inn-goose/eeprom-api-arduino/wiring/kicad/eeprom_programmer/eeprom_programmer.kicad_sch

## KiCad design wiring/kicad/eeprom_programmer/eeprom_programmer.kicad_sch (2025-12-24)

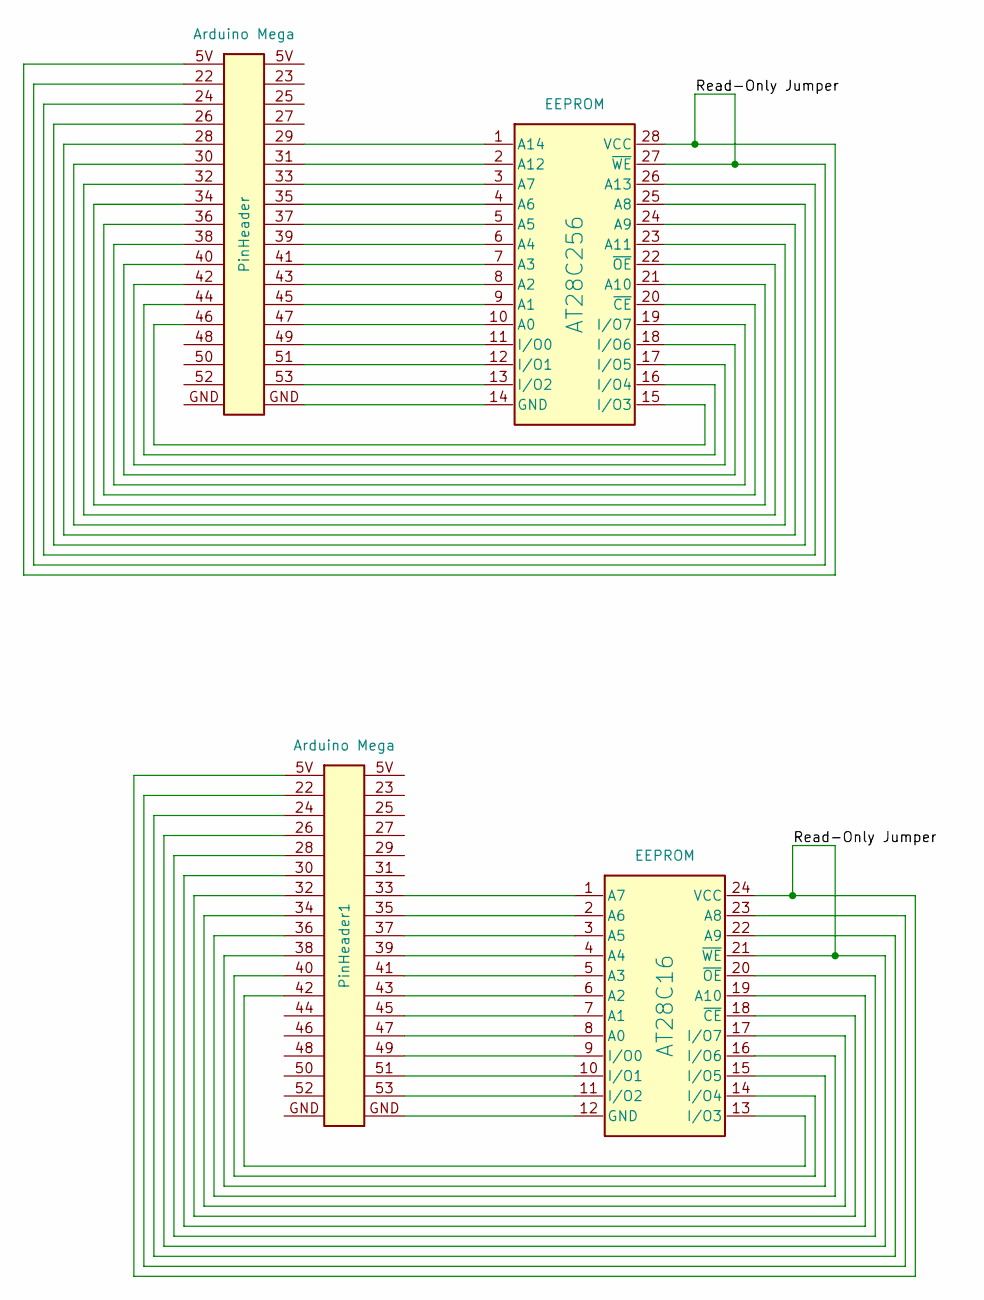
[picture p8: schematic eeprom_programmer.kicad_sch]

Parts:
AT28C16, AT28C256: EEPROM
PinHeader, PinHeader1: Arduino Mega

Connections:
unnamed: AT28C16.1 (A7), PinHeader1.33
unnamed: AT28C16.2 (A6), PinHeader1.35
unnamed: AT28C16.3 (A5), PinHeader1.37
unnamed: AT28C16.4 (A4), PinHeader1.39
unnamed: AT28C16.5 (A3), PinHeader1.41
unnamed: AT28C16.6 (A2), PinHeader1.43
unnamed: AT28C16.7 (A1), PinHeader1.45
unnamed: AT28C16.8 (A0), PinHeader1.47
unnamed: AT28C16.9 (I/O0), PinHeader1.49
unnamed: AT28C16.10 (I/O1), PinHeader1.51
unnamed: AT28C16.11 (I/O2), PinHeader1.53
unnamed: AT28C16.12 (GND), PinHeader1.GND
unnamed: AT28C16.13 (I/O3), PinHeader1.42
unnamed: AT28C16.14 (I/O4), PinHeader1.40
unnamed: AT28C16.15 (I/O5), PinHeader1.38
unnamed: AT28C16.16 (I/O6), PinHeader1.36
unnamed: AT28C16.17 (I/O7), PinHeader1.34
unnamed: AT28C16.18 (~CE), PinHeader1.32
unnamed: AT28C16.19 (A10), PinHeader1.30
unnamed: AT28C16.20 (~OE), PinHeader1.28
unnamed: AT28C16.22 (A9), PinHeader1.24
unnamed: AT28C16.23 (A8), PinHeader1.22
unnamed: AT28C256.1 (A14), PinHeader.29
unnamed: AT28C256.2 (A12), PinHeader.31
unnamed: AT28C256.3 (A7), PinHeader.33
unnamed: AT28C256.4 (A6), PinHeader.35
unnamed: AT28C256.5 (A5), PinHeader.37
unnamed: AT28C256.6 (A4), PinHeader.39
unnamed: AT28C256.7 (A3), PinHeader.41
unnamed: AT28C256.8 (A2), PinHeader.43
unnamed: AT28C256.9 (A1), PinHeader.45
unnamed: AT28C256.10 (A0), PinHeader.47
unnamed: AT28C256.11 (I/O0), PinHeader.49
unnamed: AT28C256.12 (I/O1), PinHeader.51
unnamed: AT28C256.13 (I/O2), PinHeader.53
unnamed: AT28C256.14 (GND), PinHeader.GND
unnamed: AT28C256.15 (I/O3), PinHeader.46
unnamed: AT28C256.16 (I/O4), PinHeader.44
unnamed: AT28C256.17 (I/O5), PinHeader.42
unnamed: AT28C256.18 (I/O6), PinHeader.40
unnamed: AT28C256.19 (I/O7), PinHeader.38
unnamed: AT28C256.20 (~CE), PinHeader.36
unnamed: AT28C256.21 (A10), PinHeader.34
unnamed: AT28C256.22 (~OE), PinHeader.32
unnamed: AT28C256.23 (A11), PinHeader.30
unnamed: AT28C256.24 (A9), PinHeader.28
unnamed: AT28C256.25 (A8), PinHeader.26
unnamed: AT28C256.26 (A13), PinHeader.24
Read-Only Jumper: AT28C16.21 (~WE), AT28C16.24 (VCC), AT28C256.27 (~WE), AT28C256.28 (VCC), PinHeader.5V, PinHeader.22, PinHeader1.5V, PinHeader1.26
