inn-goose/eeprom-api-arduino/eeprom_programmer/board_wiring.h

#ifndef __board_wiring_h__
#define __board_wiring_h__

namespace BoardWiring {

typedef uint8_t PIN_NO;

enum BoardWiringType : int {
  DIP28 = 1,
  DIP24 = 2,
  // unknown
  UNKNOWN = 10000
};


// ========================================
// DIP28 WIRING
// ========================================

// 29  --  1 --|    |-- 28 -- VCC
// 31  --  2 --|    |-- 27 -- 22
// 33  --  3 --|    |-- 26 -- 24
// 35  --  4 --|    |-- 25 -- 26
// 37  --  5 --|    |-- 24 -- 28
// 39  --  6 --|    |-- 23 -- 30
// 41  --  7 --|    |-- 22 -- 32
// 43  --  8 --|    |-- 21 -- 34
// 45  --  9 --|    |-- 20 -- 36
// 47  -- 10 --|    |-- 19 -- 38
// 49  -- 11 --|    |-- 18 -- 40
// 51  -- 12 --|    |-- 17 -- 42
// 53  -- 13 --|    |-- 16 -- 44
// GND -- 14 --|    |-- 15 -- 46

const PIN_NO DIP28_WIRING[28] = {
  // left side, 1-14, top-down
  29,  // 1
  31,  // 2
  33,  // 3
  35,  // 4
  37,  // 5
  39,  // 6
  41,  // 7
  43,  // 8
  45,  // 9
  47,  // 10
  49,  // 11
  51,  // 12
  53,  // 13
  0,   // 14 / GND
  // right side, 15-28, bottom-up
  46,  // 15
  44,  // 16
  42,  // 17
  40,  // 18
  38,  // 19
  36,  // 20
  34,  // 21
  32,  // 22
  30,  // 23
  28,  // 24
  26,  // 25
  24,  // 26
  22,  // 27
  0,   // 28 / VCC
};


// ========================================
// DIP24 WIRING
// ========================================

// 33  --  1 --|    |-- 24 -- VCC
// 35  --  2 --|    |-- 23 -- 22
// 37  --  3 --|    |-- 22 -- 24
// 39  --  4 --|    |-- 21 -- 26
// 41  --  5 --|    |-- 20 -- 28
// 43  --  6 --|    |-- 19 -- 30
// 45  --  7 --|    |-- 18 -- 32
// 47  --  8 --|    |-- 17 -- 34
// 49  --  9 --|    |-- 16 -- 36
// 51  -- 10 --|    |-- 15 -- 38
// 53  -- 11 --|    |-- 14 -- 40
// GND -- 12 --|    |-- 13 -- 42

const PIN_NO DIP24_WIRING[24] = {
  // left side, 1-12, top-down
  33,  // 1
  35,  // 2
  37,  // 3
  39,  // 4
  41,  // 5
  43,  // 6
  45,  // 7
  47,  // 8
  49,  // 9
  51,  // 10
  53,  // 11
  0,   // 12 / GND
  // right side, 13-24, bottom-up
  42,  // 13
  40,  // 14
  38,  // 15
  36,  // 16
  34,  // 17
  32,  // 18
  30,  // 19
  28,  // 20
  26,  // 21
  24,  // 22
  22,  // 23
  0,   // 24 / VCC
};

}  // BoardWiring

#endif  // !__board_wiring_h__
